rumsey000/Practice-of-Mechanical-Engineering/Midterm_Exam_Files/Photo/open.png

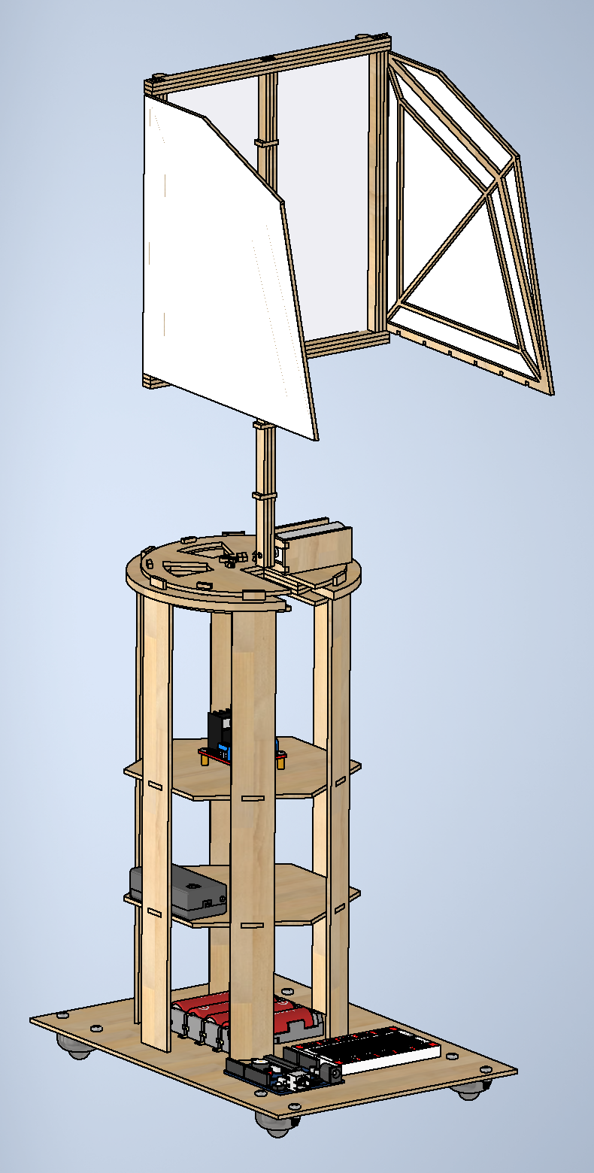
Midterm_Exam_Files/Photo/open.png
