rumsey000/Practice-of-Mechanical-Engineering/Midterm_Exam_Files/Photo/close.png

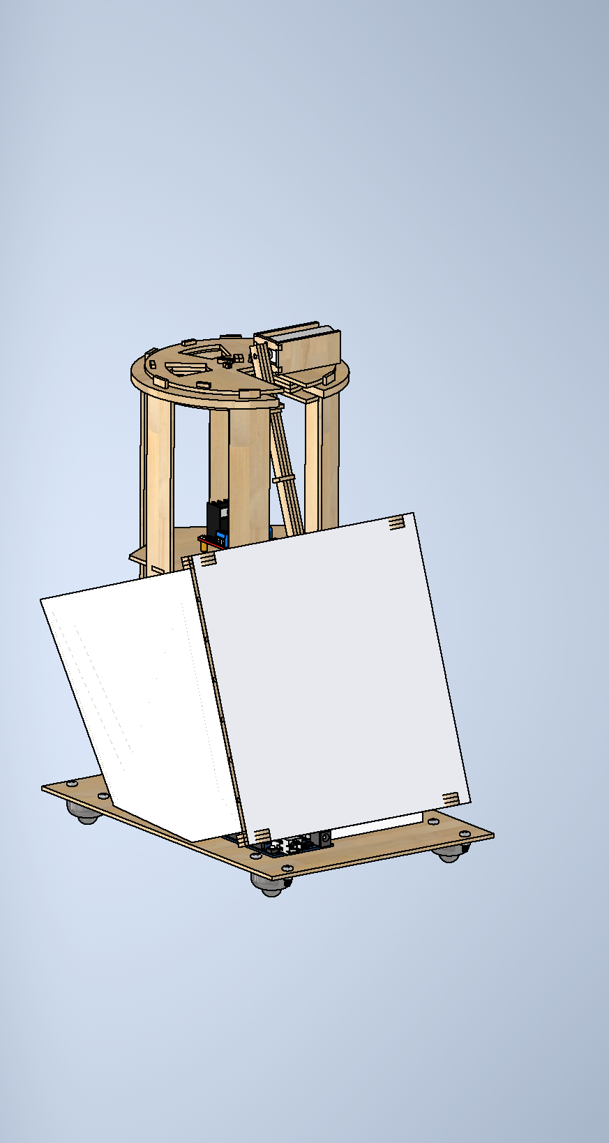
Midterm_Exam_Files/Photo/close.png
