rumsey000/Practice-of-Mechanical-Engineering/3D_CAD_Drawing/圖檔/機電設備/lm2596-dc-dc-buck-converter-module-2.snapshot.9/IMG_8608.JPG

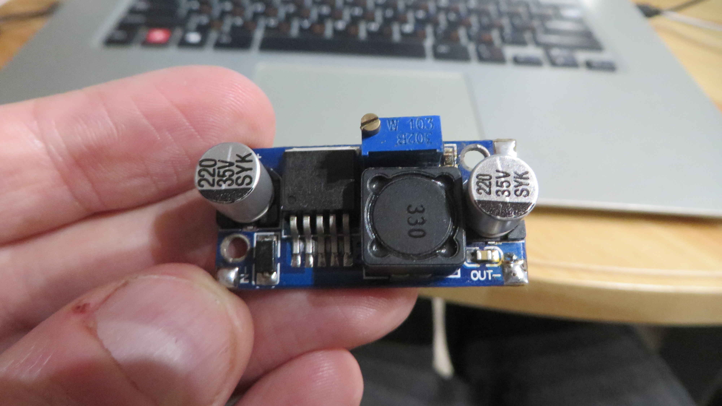
3D_CAD_Drawing/圖檔/機電設備/lm2596-dc-dc-buck-converter-module-2.snapshot.9/IMG_8608.JPG
