rumsey000/Practice-of-Mechanical-Engineering/3D_CAD_Drawing/圖檔/機電設備/lm2596-dc-dc-buck-converter-module-2.snapshot.9/LM2596 DC-DC Buck Converter Module.png

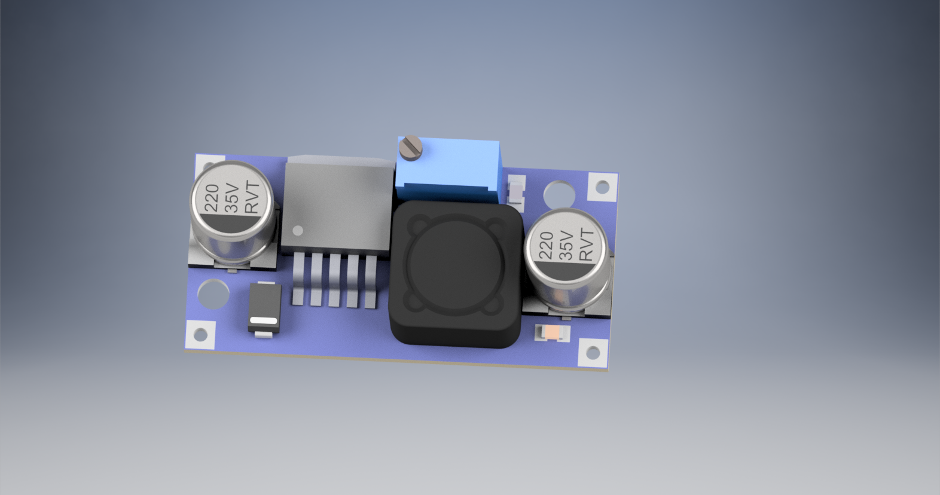
3D_CAD_Drawing/圖檔/機電設備/lm2596-dc-dc-buck-converter-module-2.snapshot.9/LM2596 DC-DC Buck Converter Module.png
