rumsey000/Practice-of-Mechanical-Engineering/Final_Exam_Files/期末報告/圖片/15度.png

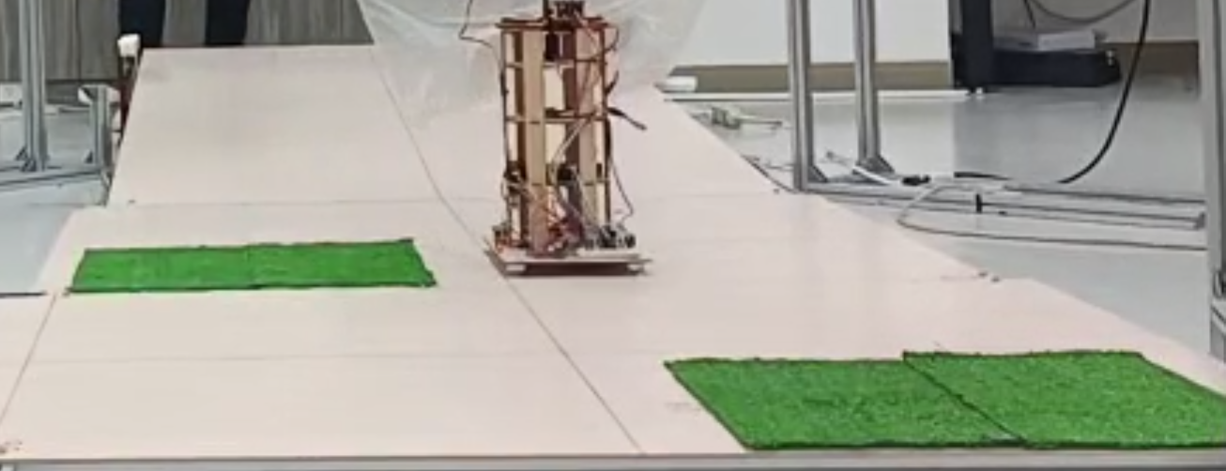
Final_Exam_Files/期末報告/圖片/15度.png
