rumsey000/Practice-of-Mechanical-Engineering/Final_Exam_Files/期末報告/圖片/測距輪模組與測距輪安裝圖，綠色者為光遮斷器，藍色箭頭為測距輪模組可自由移動的方向.png

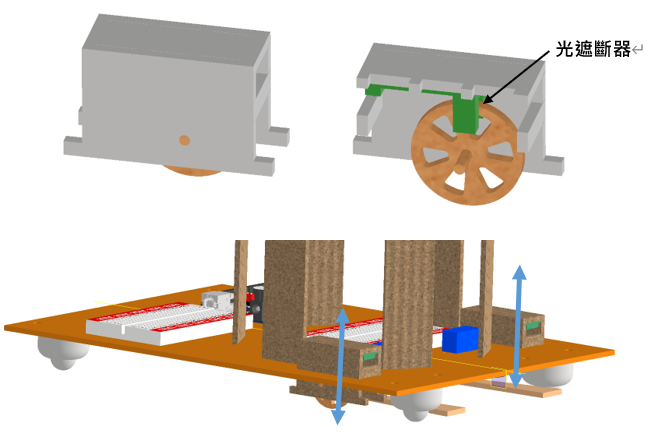
Final_Exam_Files/期末報告/圖片/測距輪模組與測距輪安裝圖，綠色者為光遮斷器，藍色箭頭為測距輪模組可自由移動的方向.png
