rumsey000/Practice-of-Mechanical-Engineering/Final_Exam_Files/期末報告/圖片/風帆與風向的關係上視圖。理想中的風帆轉角θ應該要足夠大，使得側向力大到足以使車體偏離原本軌跡。.png

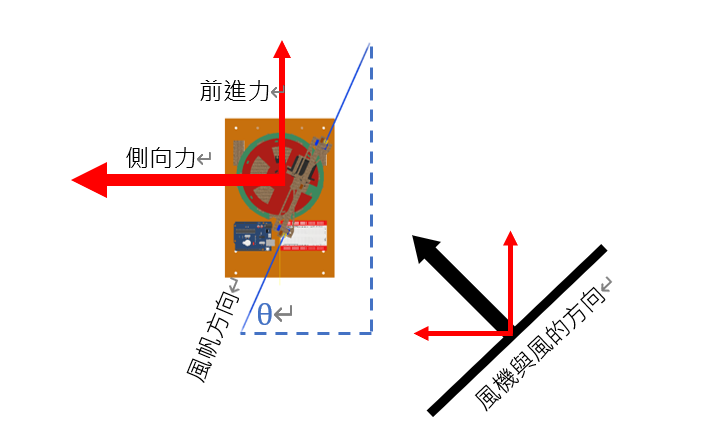
Final_Exam_Files/期末報告/圖片/風帆與風向的關係上視圖。理想中的風帆轉角θ應該要足夠大，使得側向力大到足以使車體偏離原本軌跡。.png
