rumsey000/Practice-of-Mechanical-Engineering/Midterm_Exam_Files/Photo/close2.png

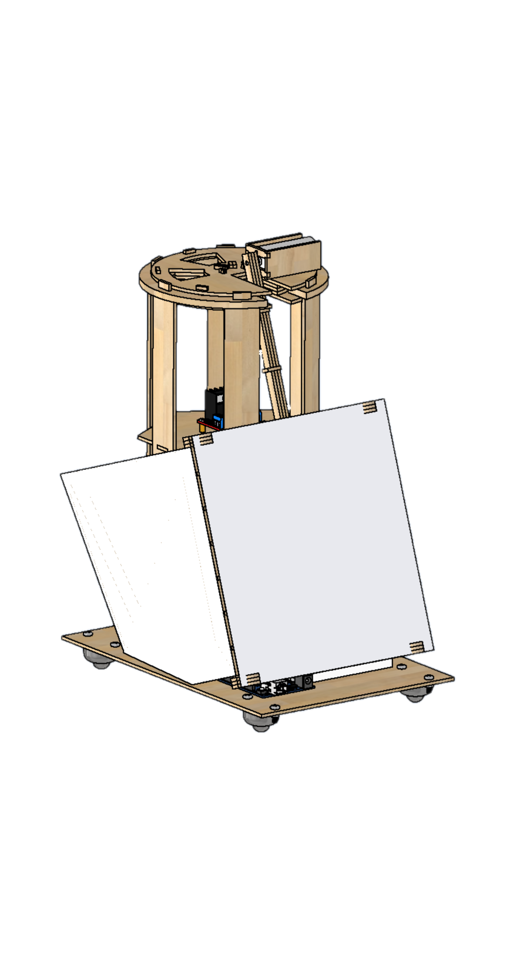
Midterm_Exam_Files/Photo/close2.png
