rumsey000/Practice-of-Mechanical-Engineering/Midterm_Exam_Files/Photo/FBD/牛眼輪平地上FBD.png

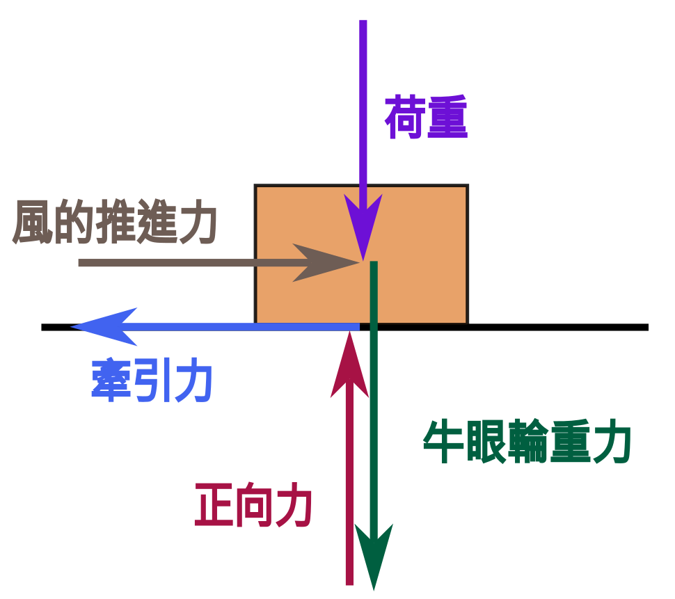
Midterm_Exam_Files/Photo/FBD/牛眼輪平地上FBD.png
