rumsey000/Practice-of-Mechanical-Engineering/Midterm_Exam_Files/Photo/open3.png

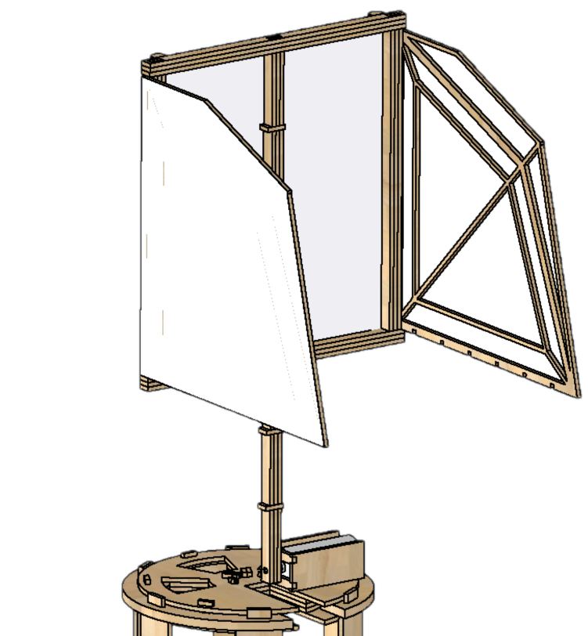
Midterm_Exam_Files/Photo/open3.png
