rumsey000/Practice-of-Mechanical-Engineering/Midterm_Exam_Files/Photo/unflod.png

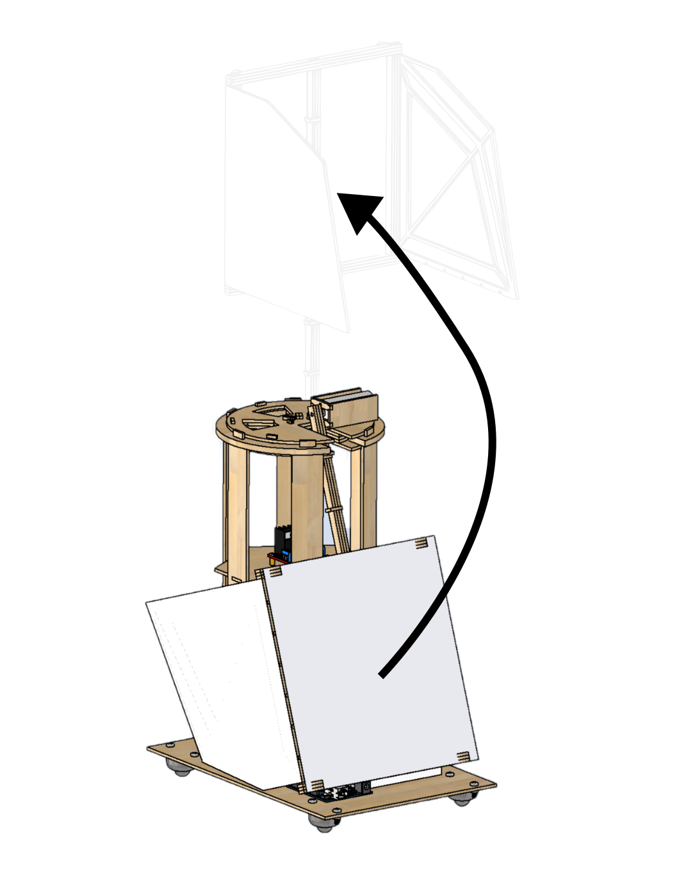
Midterm_Exam_Files/Photo/unflod.png
