rumsey000/Practice-of-Mechanical-Engineering/Midterm_Exam_Files/Photo/未命名.png

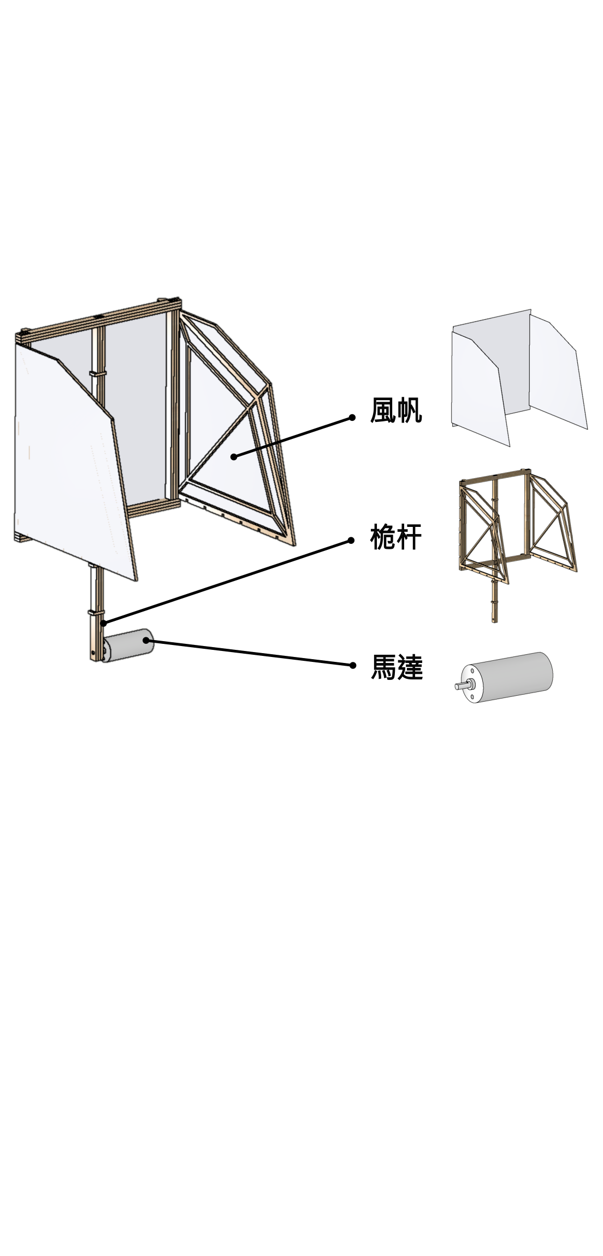
Midterm_Exam_Files/Photo/未命名.png
