rumsey000/Practice-of-Mechanical-Engineering/Midterm_Exam_Files/Photo/轉動機構.png

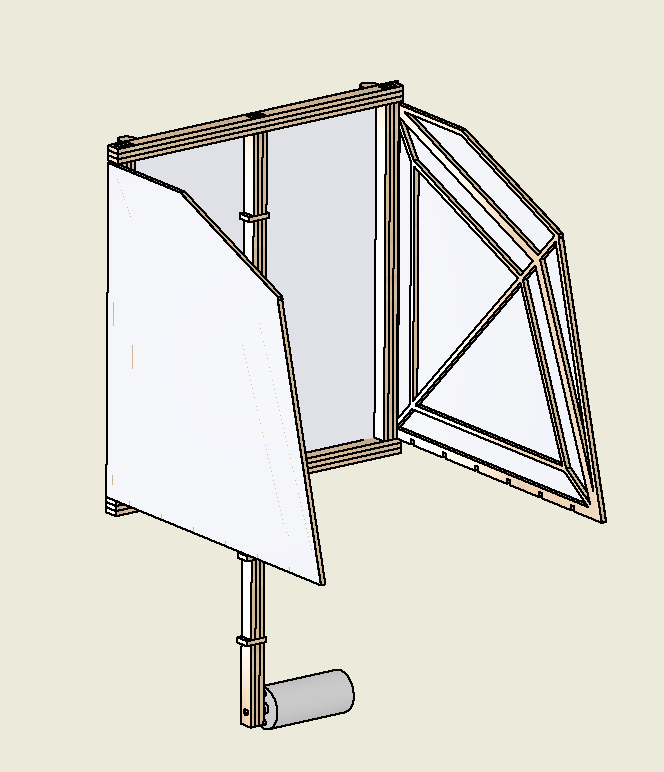
Midterm_Exam_Files/Photo/轉動機構.png
