rumsey000/Practice-of-Mechanical-Engineering/Midterm_Exam_Files/Photo/風帆2.png

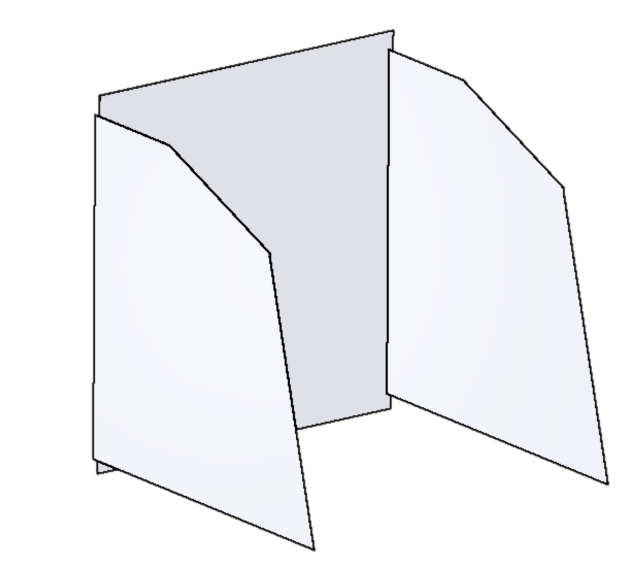
Midterm_Exam_Files/Photo/風帆2.png
