rumsey000/Practice-of-Mechanical-Engineering/接線圖/9V_battery2.png

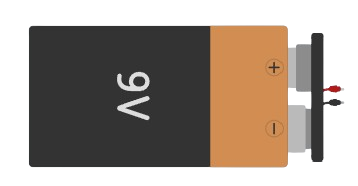
接線圖/9V_battery2.png
