rumsey000/Practice-of-Mechanical-Engineering/接線圖/18650電池盒.png

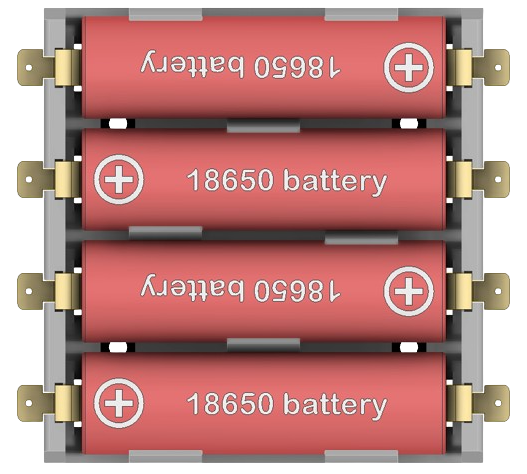
接線圖/18650電池盒.png
