rumsey000/Practice-of-Mechanical-Engineering/接線圖/AA_battery.png

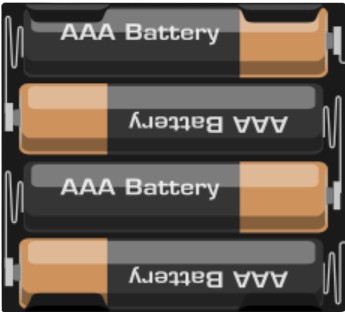
接線圖/AA_battery.png
