rumsey000/Practice-of-Mechanical-Engineering/接線圖/button.png

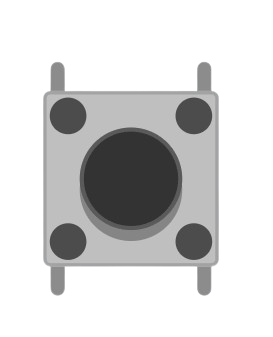
接線圖/button.png
