rumsey000/Practice-of-Mechanical-Engineering/接線圖/IMU.png

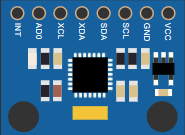
接線圖/IMU.png
