rumsey000/Practice-of-Mechanical-Engineering/接線圖/L298N.png

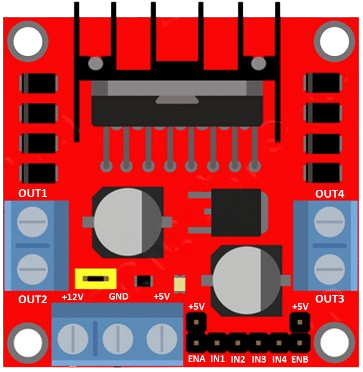
接線圖/L298N.png
