rumsey000/Practice-of-Mechanical-Engineering/接線圖/Motor_And_Encoder.png

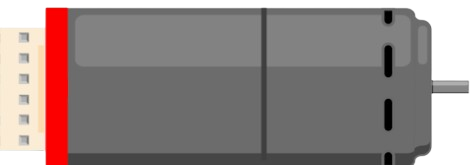
接線圖/Motor_And_Encoder.png
