rumsey000/Practice-of-Mechanical-Engineering/接線圖/servo_motor.png

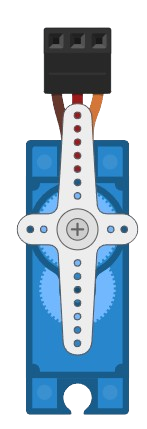
接線圖/servo_motor.png
