rumsey000/Practice-of-Mechanical-Engineering/Motor/Encoder/Encoder.ino

#include <util/atomic.h> // For the ATOMIC_BLOCK macro

#define ENCA 2 // green
#define ENCB 5 // yellow

volatile int posi = 0; // specify posi as volatile: https://www.arduino.cc/reference/en/language/variables/variable-scope-qualifiers/volatile/

void setup() {
  Serial.begin(9600);
  pinMode(ENCA,INPUT);
  pinMode(ENCB,INPUT);
  attachInterrupt(digitalPinToInterrupt(ENCA),readEncoder,RISING);
}

void loop() {
  // Read the position in an atomic block to avoid a potential
  // misread if the interrupt coincides with this code running
  // see: https://www.arduino.cc/reference/en/language/variables/variable-scope-qualifiers/volatile/
  int pos = 0; 
  ATOMIC_BLOCK(ATOMIC_RESTORESTATE) {
    pos = posi;
  }

  Serial.print(pos);
  Serial.print("\t");
  Serial.print(digitalRead(ENCA));
  Serial.print("\t");
  Serial.println(digitalRead(ENCB));
}

void readEncoder(){
  int b = digitalRead(ENCB);
  if(b > 0){
    posi++;
  }
  else{
    posi--;
  }
}
