rumsey000/Practice-of-Mechanical-Engineering/IMU/IMU_using_Kalman_filter_Calibration/IMU_using_Kalman_filter_Calibration.ino

#include "Wire.h"

///////////////////////////////////   CONFIGURATION   /////////////////////////////
//Change this 3 variables if you want to fine tune the skecth to your needs.
int buffersize=1000;     //Amount of readings used to average, make it higher to get more precision but sketch will be slower  (default:1000)
int acel_deadzone=64;     //Acelerometer error allowed, make it lower to get more precision, but sketch may not converge  (default:8)
int giro_deadzone=4;     //Giro error allowed, make it lower to get more precision, but sketch may not converge  (default:1)

uint8_t i2cData[14]; // Buffer for I2C data
int16_t ax, ay, az,gx, gy, gz ,tempRaw;

int mean_ax,mean_ay,mean_az,mean_gx,mean_gy,mean_gz,state=0;
int ax_offset,ay_offset,az_offset,gx_offset,gy_offset,gz_offset;

///////////////////////////////////   SETUP   ////////////////////////////////////
void setup() {
  // join I2C bus (I2Cdev library doesn't do this automatically)
  Wire.begin();

  // initialize serial communication
  Serial.begin(115200);

  // initialize device
  i2cData[0] = 7; // Set the sample rate to 1000Hz - 8kHz/(7+1) = 1000Hz
  i2cData[1] = 0x00; // Disable FSYNC and set 260 Hz Acc filtering, 256 Hz Gyro filtering, 8 KHz sampling
  i2cData[2] = 0x00; // Set Gyro Full Scale Range to ±250deg/s
  i2cData[3] = 0x00; // Set Accelerometer Full Scale Range to ±2g
  while (i2cWrite(0x19, i2cData, 4, false)); // Write to all four registers at once
  while (i2cWrite(0x6B, 0x01, true)); // PLL with X axis gyroscope reference and disable sleep mode
  


  // wait for ready
  while (Serial.available() && Serial.read()); // empty buffer
  while (!Serial.available()){
    Serial.println(F("Send any character to start sketch.\n"));
    delay(1500);
  }                
  while (Serial.available() && Serial.read()); // empty buffer again

  // start message
  Serial.println("\nMPU6050 Calibration Sketch");
  delay(2000);
  Serial.println("\nYour MPU6050 should be placed in horizontal position, with package letters facing up. \nDon't touch it until you see a finish message.\n");
  delay(3000);
  // verify connection
  while (i2cRead(0x75, i2cData, 1));
  if (i2cData[0] != 0x68) { // Read "WHO_AM_I" register
    Serial.print(F("Error reading sensor"));
    while (1);
  }
  delay(1000);
  // reset offsets
  ax_offset = 0;
  ay_offset = 0;
  az_offset = 0;
  gx_offset = 0;
  gy_offset = 0;
  gz_offset = 0;
}

///////////////////////////////////   LOOP   ////////////////////////////////////
void loop() {
  if (state==0){
    Serial.println("\nReading sensors for first time...");
    meansensors();
    state++;
    delay(1000);
  }

  if (state==1) {
    Serial.println("\nCalculating offsets...");
    calibration();
    state++;
    delay(1000);
  }

  if (state==2) {
    meansensors();
    Serial.println("\nFINISHED!");
    Serial.print("\nSensor readings with offsets:\t");
    Serial.print(mean_ax); 
    Serial.print("\t");
    Serial.print(mean_ay); 
    Serial.print("\t");
    Serial.print(mean_az); 
    Serial.print("\t");
    Serial.print(mean_gx); 
    Serial.print("\t");
    Serial.print(mean_gy); 
    Serial.print("\t");
    Serial.println(mean_gz);
    Serial.print("Your offsets:\t");
    Serial.print(ax_offset); 
    Serial.print("\t");
    Serial.print(ay_offset); 
    Serial.print("\t");
    Serial.print(az_offset); 
    Serial.print("\t");
    Serial.print(gx_offset); 
    Serial.print("\t");
    Serial.print(gy_offset); 
    Serial.print("\t");
    Serial.println(gz_offset); 
    Serial.println("\nData is printed as: acelX acelY acelZ giroX giroY giroZ");
    Serial.println("Check that your sensor readings are close to 0 0 16384 0 0 0");
    Serial.println("If calibration was succesful write down your offsets so you can set them in your projects using something similar to mpu.setXAccelOffset(youroffset)");
    while (1);
  }
}

///////////////////////////////////   FUNCTIONS   ////////////////////////////////////
void meansensors(){
  long i=0,buff_ax=0,buff_ay=0,buff_az=0,buff_gx=0,buff_gy=0,buff_gz=0;

  while (i<(buffersize+101)){
    // read raw accel/gyro measurements from device
    while (i2cRead(0x3B, i2cData, 14));
    ax = (int16_t)((i2cData[0] << 8) | i2cData[1]);
    ay = (int16_t)((i2cData[2] << 8) | i2cData[3]);
    az = (int16_t)((i2cData[4] << 8) | i2cData[5]);
    tempRaw = (int16_t)((i2cData[6] << 8) | i2cData[7]);
    gx = (int16_t)((i2cData[8] << 8) | i2cData[9]);
    gy = (int16_t)((i2cData[10] << 8) | i2cData[11]);
    gz = (int16_t)((i2cData[12] << 8) | i2cData[13]);
    // plus offset
    ax = ax + ax_offset;
    ay = ay + ay_offset;
    az = az + az_offset;
    gx = gx + gx_offset;
    gy = gy + gy_offset;
    gz = gz + gz_offset;
    if (i>100 && i<=(buffersize+100)){ //First 100 measures are discarded
      buff_ax=buff_ax+ax;
      buff_ay=buff_ay+ay;
      buff_az=buff_az+az;
      buff_gx=buff_gx+gx;
      buff_gy=buff_gy+gy;
      buff_gz=buff_gz+gz;
    }
    if (i==(buffersize+100)){
      mean_ax=buff_ax/buffersize;
      mean_ay=buff_ay/buffersize;
      mean_az=buff_az/buffersize;
      mean_gx=buff_gx/buffersize;
      mean_gy=buff_gy/buffersize;
      mean_gz=buff_gz/buffersize;
    }
    i++;
    delay(2); //Needed so we don't get repeated measures
  }
}

void calibration(){
  ax_offset=-mean_ax;
  ay_offset=-mean_ay;
  az_offset=(16384-mean_az);

  gx_offset=-mean_gx;
  gy_offset=-mean_gy;
  gz_offset=-mean_gz;
  while (1){
    int ready=0;
    meansensors();
    Serial.println("...");

    if (abs(mean_ax)<=acel_deadzone) ready++;
    else ax_offset=ax_offset-mean_ax/acel_deadzone;

    if (abs(mean_ay)<=acel_deadzone) ready++;
    else ay_offset=ay_offset-mean_ay/acel_deadzone;

    if (abs(16384-mean_az)<=acel_deadzone) ready++;
    else az_offset=az_offset+(16384-mean_az)/acel_deadzone;

    if (abs(mean_gx)<=giro_deadzone) ready++;
    else gx_offset=gx_offset-mean_gx/(giro_deadzone+1);

    if (abs(mean_gy)<=giro_deadzone) ready++;
    else gy_offset=gy_offset-mean_gy/(giro_deadzone+1);

    if (abs(mean_gz)<=giro_deadzone) ready++;
    else gz_offset=gz_offset-mean_gz/(giro_deadzone+1);

    if (ready==6) break;
  }
}
